kritzikratzi/Stepsie-Pixie/arduino/stepsie_sketch/icons.ino

const unsigned char icon_tri_next[] PROGMEM = {
    B00000000,
    B00010000,
    B00110000,
    B01111110,
    B00110000,
    B00010000,
    B00000000,
    B00000000
};

/*
const unsigned char icon_tri_down[] PROGMEM = {
    B00000000,
    B00001000,
    B00011000,
    B00111000,
    B00011000,
    B00001000,
    B00000000,
    B00000000
};

const unsigned char icon_tri_up[] PROGMEM = {
    B00000000,
    B00100000,
    B00110000,
    B00111000,
    B00110000,
    B00100000,
    B00000000,
    B00000000
};
*/

const unsigned char icon_tri_down[] PROGMEM = {
    B00000000,
    B00001000,
    B00001000,
    B00001000,
    B00001000,
    B00001000,
    B00000000,
    B00000000
};

const unsigned char icon_tri_up[] PROGMEM = {
    B00000000,
    B00001000,
    B00001000,
    B00111110,
    B00001000,
    B00001000,
    B00000000,
    B00000000
};
